lcismondi/Enclosure3D/Carcasa/Imagenes/Carcaza Enclosure3D v10 4.png

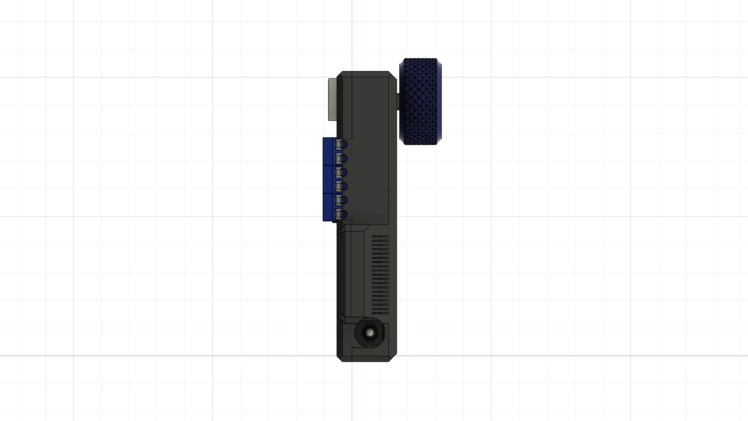
Carcasa/Imagenes/Carcaza Enclosure3D v10 4.png
